fdev31/keypass/src/indexPage.h

#ifndef _INDEXPAGE_H
#define _INDEXPAGE_H
#include <Arduino.h>
#include <stdint.h>
#include <stddef.h>
const size_t index_html_gz_len = 7565;
const uint8_t index_html[7565] PROGMEM = {
0x1f, 0x8b, 0x08, 0x08, 0x08, 0xaf, 0xe2, 0x68, 0x02, 0x03, 0x69, 0x6e, 0x64, 0x65, 0x78, 0x2e,
0x68, 0x74, 0x6d, 0x6c, 0x00, 0xc4, 0x3c, 0x7b, 0x7f, 0x9b, 0x46, 0xb6, 0xff, 0xf3, 0x29, 0x26,
0x24, 0x75, 0xa0, 0x91, 0x64, 0x49, 0xb1, 0x13, 0x07, 0x8c, 0x5c, 0xe7, 0xd5, 0xb8, 0x9b, 0xd7,
0x8d, 0x9d, 0x76, 0xf7, 0xe6, 0x97, 0x1b, 0x23, 0x18, 0x49, 0x24, 0x08, 0x28, 0x20, 0xcb, 0xaa,
0xac, 0xfd, 0xec, 0xf7, 0x9c, 0x79, 0xc0, 0xf0, 0x90, 0xed, 0x76, 0xd3, 0x7b, 0xb7, 0x5b, 0x59,
0x0c, 0x33, 0x67, 0xce, 0xfb, 0x35, 0xa3, 0x1e, 0xde, 0x79, 0xfe, 0xee, 0xd9, 0xd9, 0xbf, 0xde,
0xbf, 0x20, 0xb3, 0x7c, 0x1e, 0x8e, 0xb4, 0x43, 0xf9, 0x87, 0xba, 0x3e, 0xfc, 0xc9, 0x83, 0x3c,
0xa4, 0xa3, 0x7f, 0xd0, 0xd5, 0x7b, 0x37, 0xcb, 0x0e, 0x77, 0xf9, 0xa3, 0x76, 0x38, 0xa7, 0xb9,
0x4b, 0x22, 0x77, 0x4e, 0x1d, 0xfd, 0x22, 0xa0, 0xcb, 0x24, 0x4e, 0x73, 0x9d, 0x78, 0x71, 0x94,
0xd3, 0x28, 0x77, 0xf4, 0x65, 0xe0, 0xe7, 0x33, 0xc7, 0xa7, 0x17, 0x81, 0x47, 0xbb, 0xec, 0xa1,
0x43, 0x82, 0x28, 0xc8, 0x03, 0x37, 0xec, 0x66, 0x9e, 0x1b, 0x52, 0x67, 0xd0, 0xeb, 0xeb, 0x64,
0x17, 0x00, 0x85, 0x41, 0xf4, 0x4d, 0x4b, 0x69, 0xe8, 0xe8, 0x59, 0xbe, 0x0a, 0x69, 0x36, 0xa3,
0x34, 0xd7, 0xb5, 0x59, 0x4a, 0x27, 0x8e, 0x3e, 0xcb, 0xf3, 0x24, 0xb3, 0x76, 0x77, 0x27, 0x00,
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
0x83, 0x9a, 0x0b, 0x8f, 0x05, 0x0f, 0xc0, 0x5a, 0xdd, 0x3c, 0xb8, 0x40, 0x85, 0xbb, 0xa0, 0xe9,
0x24, 0x44, 0x05, 0x9c, 0x05, 0xbe, 0x4f, 0xa3, 0x82, 0x3e, 0xcb, 0x1a, 0x53, 0x10, 0x0b, 0xb2,
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
};
#endif
