fdev31/keypass/src/password.cpp

#include "password.h"
#include "Preferences.h"
#include "WString.h"
#include "configuration.h"
#include "constants.h"
#include "crypto.h"
#include "graphics.h"
#include "hid.h"
#include "importexport.h"
#include "main.h"
#include "restore.h"
#include "settings.h"
#include "streamadapter.h"
#include "utils.h"
#include <Arduino.h>
#include <ESPAsyncWebServer.h>
#include <cstring>
#include <stdio.h>
#include <stdlib.h>
#include <string.h>
#include <time.h>
#include <unistd.h>

// Core business logic functions (independent of AsyncWebServerRequest)

Password password;

static Password readPassword(int id) {
#if USE_EEPROM_API
  Password password;
  int address = id * sizeof(Password);
  EEPROM.get(address, password);
  // Add validation check to ensure data is valid
  if (password.name[0] == 0xFF) { // EEPROM default state is 0xFF
    password.name[0] = '\0';      // Mark as empty
  }
  return password;
#else
  uint8_t passBuffer[MAX_PASS_LEN];
  uint8_t nonce[NONCE_LEN];
  Preferences preferences;
  const char *key = mkEntryName(id);
  preferences.begin(key, true);
  if (preferences.isKey(F_NAME) == false) {
    preferences.end();
    Password empty_password;
    empty_password.name[0] = '\0'; // No password found
    return empty_password;
  }
  int pass_version = preferences.getInt(F_FORMAT, -1);
  if (pass_version == 1) {
    strlcpy(password.name, preferences.getString(F_NAME).c_str(), MAX_NAME_LEN);
    preferences.getBytes(F_PASSWORD, passBuffer, MAX_PASS_LEN);
    preferences.getBytes(F_NONCE, nonce, NONCE_LEN);
    password.layout = preferences.getInt(F_LAYOUT);
  }
  preferences.end();

  if (pass_version == -1) {
    password.name[0] = '\0'; // No password found
  }

  switch (pass_version) {
  case 0:
    strlcpy((char *)password.password, (char *)passBuffer, MAX_PASS_LEN);
    break;
  case 1:
    decryptBuffer((uint8_t *)passBuffer, (char *)password.password,
                  MAX_PASS_LEN, nonce);
    break;
  }
  memset(passBuffer, 0, MAX_PASS_LEN);
  return password;
#endif
}

static void clearPassword(int id) {
  Preferences preferences;
  preferences.begin(mkEntryName(id), false);
  preferences.clear();
  preferences.end();
}

static void writePassword(int id, const Password &password) {
#if USE_EEPROM_API
  int address = id * sizeof(Password);
  EEPROM.put(address, password);
  EEPROM.commit();
#else
  uint8_t *nonce = getNonce();
  int pass_len = strlen((const char *)password.password);
  static uint8_t encrypted_password[MAX_PASS_LEN];
  Preferences preferences;

  preferences.begin(mkEntryName(id), false);
  preferences.putString(F_NAME, password.name);
  randomizeBuffer((uint8_t *)password.password + pass_len + 1,
                  MAX_PASS_LEN - pass_len - 1);
  encryptBuffer((char *)password.password, encrypted_password, MAX_PASS_LEN,
                nonce);
  preferences.putBytes(F_PASSWORD, encrypted_password, MAX_PASS_LEN);
  preferences.putBytes(F_NONCE, nonce, NONCE_LEN);
  preferences.putInt(F_FORMAT, FORMAT_VERSION);
  preferences.putInt(F_LAYOUT, password.layout);
  preferences.end();
  memset(encrypted_password, 0, MAX_PASS_LEN);
#endif
}

static void sendAnyKeymap(const char *text, int layout, int newline) {
  if (layout == -1) {
    while (*text) {
      sendKey(*text++, true);
    }

  } else {
    while (*text) {
      sendKeymap(*text++, layout);
      delay(50);
    }
  }
  if (newline) {
    sendKey('\n', false); // Send newline if requested
  }
}

bool typeRawText(const char *text, int layout, bool sendNewline) {
  if (text == nullptr)
    return false;

  ping();
  sendAnyKeymap(text, layout, sendNewline);
  return true;
}

bool typePassword(int id, int layout, bool sendNewline) {
  if (id < 0 || id >= MAX_PASSWORDS)
    return false;

  ping();

  // #ifdef ENABLE_GRAPHICS
  //   printText(1, "Typing");
  // #endif
  password = readPassword(id);
  char *text = (char *)password.password;

  // If layout is specified, use it; otherwise use the stored layout
  int effectiveLayout = (layout != -1) ? layout : password.layout;

  sendAnyKeymap(text, effectiveLayout, sendNewline);
  memset(password.password, 0, MAX_PASS_LEN);
  // #ifdef ENABLE_GRAPHICS
  //   printText(1, "Typed");
  // #endif
  return true;
}

const char *fetchPassword(int id) {
  if (id < 0 || id >= MAX_PASSWORDS)
    return nullptr;

  ping();
  password = readPassword(id);
  return (char *)password.password;
}

void clearFetchedPassword() { memset(password.password, 0, MAX_PASS_LEN); }

bool editPassword(int id, const char *name, const char *clear_pass,
                  int layout) {
  if (id < 0 || id >= MAX_PASSWORDS)
    return false;

  ping();

  password = readPassword(id);

  // Update fields if provided
  if (layout != -2) { // -2 means "don't change"
    password.layout = layout;
  }

  if (name != nullptr) {
    strlcpy(password.name, name, MAX_NAME_LEN);
  }

  if (clear_pass != nullptr) {
    strlcpy((char *)password.password, clear_pass, MAX_PASS_LEN);
  }

  // Save the updated password
  writePassword(id, password);
  memset(password.password, 0, MAX_PASS_LEN);
  return true;
}

String listPasswords() {
  ping();

  // Create a dynamic JSON string to hold the list of passwords
  String json = "{\"passwords\":[";

  // Loop through password ids and add existing passwords to the JSON
  bool firstItem = true;
  for (int id = 0; id < MAX_PASSWORDS; id++) {
    password = readPassword(id);
    if (password.name[0] == '\0')
      break;

    if (!firstItem) {
      json += ",";
    }
    json += "{\"name\":\"" + String(password.name) +
            "\",\"uid\":" + String(id) +
            ",\"layout\":" + String(password.layout) +
            ",\"len\":" + strlen((char *)password.password) + "}";
    firstItem = false;
  }
  clearFetchedPassword();

  Preferences prefs;
  size_t entries_left = prefs.freeEntries();
  json += String("], \"free\":") + entries_left + "}";

  return json;
}

void factoryReset() {
  ping();
  // #ifdef ENABLE_GRAPHICS
  //   printText(1, "Reset");
  // #endif
  Preferences preferences;

  for (int id = 0; id < MAX_PASSWORDS; id++) {
    clearPassword(id);
  }

#if not USE_EEPROM_API
  factoryResetSettings();
#elif
#pragma message "EEPROM API is used, factory reset not implemented for settings"
#endif
}

bool setupPassphrase(const char *phrase) {
  if (phrase == nullptr)
    return false;
  ping();
  return setPassPhrase(phrase);
}

bool dumpOnePassword(int id, StringStreamAdapter &pString) {
  Password password = readPassword(id);
  if (!password.name[0]) {
    return false;
  }

  dumpSinglePassword(pString, password.name, (const char *)password.password,
                     password.layout, getNonce());
  memset(password.password, 0, MAX_PASS_LEN);
  return true;
}

void dumpPasswords(StringStreamAdapter *stream) {
  ping();
  stream->write(DUMP_START "\n");

  StringStreamAdapter pString;

  bool endReached = false;
  for (int id = 0; !endReached && id < MAX_PASSWORDS; id++) {
    pString.clear();
    if (!dumpOnePassword(id, pString)) {
      endReached = true;
      break;
    }
    stream->write(pString.c_str());
    stream->write("\n");
  }
  stream->write(DUMP_END "\n");
}

static int savePassCount = 0;

void savePassData(const char *name, const char *passwordData, int layout,
                  int slot, uint8_t *nonce) {
  editPassword(slot, name, passwordData, layout);
  savePassCount++;
}

String restoreMCUPasswords(const String &data) {
  savePassCount = 0;
  restorePasswords(data, savePassData, true);
  return String("Restored ") + String(savePassCount) +
         " passwords successfully.";
}
