fdev31/keypass/src/captive.cpp

#include "settings.h"
#include "configuration.h"
#include <WiFi.h>
#include <string.h>

// Captive Portal
#include "main.h"
#include <AsyncTCP.h> //https://github.com/me-no-dev/AsyncTCP using the latest dev version from @me-no-dev
#include <DNSServer.h>
#include <ESPAsyncWebServer.h> //https://github.com/me-no-dev/ESPAsyncWebServer using the latest dev version from @me-no-dev
#include <esp_wifi.h>          //Used for mpdu_rx_disable android workaround

// Pre reading on the fundamentals of captive portals
// https://textslashplain.com/2022/06/24/captive-portals/

static const IPAddress localIP(4, 3, 2,
                               1); // the IP address the web server, Samsung
                                   // requires the IP to be in public space
static const IPAddress gatewayIP(4, 3, 2,
                                 1); // IP address of the network should be the
                                     // same as the local IP for captive portals
static const IPAddress subnetMask(255, 255, 255, 0);

static const String localIPURL = "http://4.3.2.1";

DNSServer dnsServer;
AsyncWebServer server(80);

void setUpDNSServer(const char *ssid, const char *password,
                    DNSServer &dnsServer, const IPAddress &localIP) {

  // Set the TTL for DNS response and start the DNS server
  dnsServer.setTTL(3600);
  dnsServer.start(53, "*", localIP);
}

void startSoftAccessPoint(const char *wifi_ssid, const char *wifi_password,
                          const IPAddress &localIP,
                          const IPAddress &gatewayIP) {
  // Define the WiFi channel to be used (channel 6 in this case)
#define WIFI_CHANNEL 6

  // Set the WiFi mode to access point and station
  WiFi.mode(WIFI_MODE_AP);

  // Define the subnet mask for the WiFi network
  const IPAddress subnetMask(255, 255, 255, 0);

  // Configure the soft access point with a specific IP and subnet mask
  WiFi.softAPConfig(localIP, gatewayIP, subnetMask);

  // Start the soft access point with the given ssid, password, channel, max
  // number of clients
  WiFi.softAP(wifi_ssid, wifi_password, WIFI_CHANNEL, 0, MAX_CLIENTS);

  // Disable AMPDU RX on the ESP32 WiFi to fix a bug on Android
  esp_wifi_stop();
  esp_wifi_deinit();
  wifi_init_config_t my_config = WIFI_INIT_CONFIG_DEFAULT();
  my_config.ampdu_rx_enable = false;
  esp_wifi_init(&my_config);
  esp_wifi_start();
  vTaskDelay(100 / portTICK_PERIOD_MS); // Add a small delay
}

void setUpWebserver(AsyncWebServer &server, const IPAddress &localIP) {
  //======================== Webserver ========================
  // WARNING IOS (and maybe macos) WILL NOT POP UP IF IT CONTAINS THE WORD
  // "Success" https://www.esp8266.com/viewtopic.php?f=34&t=4398 SAFARI (IOS) IS
  // STUPID, G-ZIPPED FILES CAN'T END IN .GZ
  // https://github.com/homieiot/homie-esp8266/issues/476 this is fixed by the
  // webserver serve static function. SAFARI (IOS) there is a 128KB limit to the
  // size of the HTML. The HTML can reference external resources/images that
  // bring the total over 128KB SAFARI (IOS) popup browser has some severe
  // limitations (javascript disabled, cookies disabled)

  // Required
  server.on("/connecttest.txt", [](AsyncWebServerRequest *request) {
    request->redirect("http://logout.net");
    ping();
  }); // windows 11 captive portal workaround
  server.on("/wpad.dat", [](AsyncWebServerRequest *request) {
    request->send(404);
  }); // Honestly don't understand what this is but a 404 stops win 10 keep
      // calling this repeatedly and panicking the esp32 :)

  // Background responses: Probably not all are Required, but some are. Others
  // might speed things up? A Tier (commonly used by modern systems)
  server.on("/generate_204", [](AsyncWebServerRequest *request) {
    request->redirect(localIPURL);
    ping();
  }); // android captive portal redirect
  server.on("/redirect", [](AsyncWebServerRequest *request) {
    request->redirect(localIPURL);
    ping();
  }); // microsoft redirect
  server.on("/hotspot-detect.html", [](AsyncWebServerRequest *request) {
    request->redirect(localIPURL);
    ping();
  }); // apple call home
  server.on("/canonical.html", [](AsyncWebServerRequest *request) {
    request->redirect(localIPURL);
    ping();
  }); // firefox captive portal call home
  server.on("/success.txt", [](AsyncWebServerRequest *request) {
    request->send(200);
    ping();
  }); // firefox captive portal call home
  server.on("/ncsi.txt", [](AsyncWebServerRequest *request) {
    request->redirect(localIPURL);
    ping();
  }); // windows call home

  // return 404 to webpage icon
  server.on("/favicon.ico", [](AsyncWebServerRequest *request) {
    request->send(404);
    ping();
  }); // webpage icon
  //

  // the catch all
  server.onNotFound([](AsyncWebServerRequest *request) {
    ping();
    request->redirect(localIPURL);
  });
};
static void handleWifiEvent(void *arg, esp_event_base_t event_base,
                            int32_t event_id, void *event_data) {
  if (event_base == WIFI_EVENT) {
    switch (event_id) {
    case WIFI_EVENT_AP_STACONNECTED:
    case WIFI_EVENT_AP_STADISCONNECTED:
    case WIFI_EVENT_AP_START:
      ping(); // Reset sleeping state
      break;
    }
  }
}

void captiveSetup() {
  String password = getWifiPassword();
  startSoftAccessPoint(DEFAULT_WIFI_SSID, password.c_str(), localIP, gatewayIP);
  setUpDNSServer(DEFAULT_WIFI_SSID, password.c_str(), dnsServer, localIP);
  setUpWebserver(server, localIP);
  server.begin();
  //
  esp_event_handler_register(WIFI_EVENT, ESP_EVENT_ANY_ID, &handleWifiEvent,
                             NULL); // Register event handler
}
void captiveLoop() {
  dnsServer.processNextRequest(); // I call this at least every 10ms in my other
}
