fdev31/keypass/src/keymap.cpp

#include "keymap.h"// FR keyboard layout
static const KeyMapping LAYOUT_FR[] = {
    {'\t', 43, 0},  // Tab
    {'\n', 40, 0},  // Enter
    {' ', 44, 0},    // Space
    {60, 100, 0}, // <
    {62, 100, 2}, // >
    {113, 4, 0}, // q
    {81, 4, 2}, // Q
    {98, 5, 0}, // b
    {66, 5, 2}, // B
    {99, 6, 0}, // c
    {67, 6, 2}, // C
    {100, 7, 0}, // d
    {68, 7, 2}, // D
    {101, 8, 0}, // e
    {69, 8, 2}, // E
    {102, 9, 0}, // f
    {70, 9, 2}, // F
    {103, 10, 0}, // g
    {71, 10, 2}, // G
    {104, 11, 0}, // h
    {72, 11, 2}, // H
    {105, 12, 0}, // i
    {73, 12, 2}, // I
    {106, 13, 0}, // j
    {74, 13, 2}, // J
    {107, 14, 0}, // k
    {75, 14, 2}, // K
    {108, 15, 0}, // l
    {76, 15, 2}, // L
    {44, 16, 0}, // ,
    {63, 16, 2}, // ?
    {110, 17, 0}, // n
    {78, 17, 2}, // N
    {111, 18, 0}, // o
    {79, 18, 2}, // O
    {112, 19, 0}, // p
    {80, 19, 2}, // P
    {97, 20, 0}, // a
    {65, 20, 2}, // A
    {114, 21, 0}, // r
    {82, 21, 2}, // R
    {115, 22, 0}, // s
    {83, 22, 2}, // S
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
    {0, 0, 0}  // End marker
};

// US keyboard layout
static const KeyMapping LAYOUT_US[] = {
    {'\t', 43, 0},  // Tab
    {'\n', 40, 0},  // Enter
    {' ', 44, 0},    // Space
    {97, 4, 0}, // a
    {65, 4, 2}, // A
    {98, 5, 0}, // b
    {66, 5, 2}, // B
    {99, 6, 0}, // c
    {67, 6, 2}, // C
    {100, 7, 0}, // d
    {68, 7, 2}, // D
    {101, 8, 0}, // e
    {69, 8, 2}, // E
    {102, 9, 0}, // f
    {70, 9, 2}, // F
    {103, 10, 0}, // g
    {71, 10, 2}, // G
    {104, 11, 0}, // h
    {72, 11, 2}, // H
    {105, 12, 0}, // i
    {73, 12, 2}, // I
    {106, 13, 0}, // j
    {74, 13, 2}, // J
    {107, 14, 0}, // k
    {75, 14, 2}, // K
    {108, 15, 0}, // l
    {76, 15, 2}, // L
    {109, 16, 0}, // m
    {77, 16, 2}, // M
    {110, 17, 0}, // n
    {78, 17, 2}, // N
    {111, 18, 0}, // o
    {79, 18, 2}, // O
    {112, 19, 0}, // p
    {80, 19, 2}, // P
    {113, 20, 0}, // q
    {81, 20, 2}, // Q
    {114, 21, 0}, // r
    {82, 21, 2}, // R
    {115, 22, 0}, // s
    {83, 22, 2}, // S
    {116, 23, 0}, // t
    {84, 23, 2}, // T
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
    {0, 0, 0}  // End marker
};

// Array of pointers to keyboard layouts for easy access
const KeyMapping* KEYBOARD_LAYOUTS[] = {
    LAYOUT_FR,
    LAYOUT_US
};
