fdev31/keypass/src/constants.h

// constants.h
#ifndef _CONSTANTS_H
#define _CONSTANTS_H

#define FORMAT_VERSION 1

// TODO: measure the maximum acceptable number more accurately
#define MAX_PASSWORDS 100
#define STORED_PASSWD_BLOCKS 2

// Crypto constants
#define STO_BLOCK_SIZE 16
#define RAND_BYTE_FACTOR RAND_MAX / 255

#define CRYPTO_HEADER_SIZE 2 // salt + layout

#define META_SIZE 32
#define NONCE_LEN 12
#define MAX_NAME_LEN META_SIZE - CRYPTO_HEADER_SIZE
#define MAX_PASS_LEN (STORED_PASSWD_BLOCKS * 16)

#define CRYPTO_OVERHEAD 0
#define UNENCRYPTED_DATA_LENGTH 1 + NONCE_LEN // version + nonce

// Encrypted dump length
#define DUMP_LENGTH (META_SIZE + MAX_PASS_LEN + CRYPTO_OVERHEAD)
static_assert(DUMP_LENGTH % STO_BLOCK_SIZE == 0,
              "DUMP_LENGTH must be a multiple of STO_BLOCK_SIZE");

// Preferences fields
#define F_NAMESPACE "KeyPass" // used for global settings
#define DEVICE_NAME_KEY "device_name"
#define WIFI_PASSWORD_KEY "wifi_password"
#define MAGIC_KEY_KEY "magic_key"
// password entry properties
#define F_NAME "name"
#define F_PASSWORD "password"
#define F_FORMAT "v"
#define F_LAYOUT "layout"
#define F_NONCE "n"

#define DUMP_START "#KPDUMP"
#define DUMP_END "#/KPDUMP"

#endif // CONSTANTS_H
