fdev31/keypass/src/icons.cpp

// Generated bitmap icons implementation
#include "icons.h"

// Bitmap data for icon_bluetooth.png (20x20)
const uint8_t icon_bluetooth_data[] = {
    0x00, 0x00, 0x00, 0x00, 0x06, 0x00, 0x00, 0x0E, 0x00, 0x00, 0x1E, 0x00,
    0x00, 0x36, 0x00, 0x30, 0xE6, 0x00, 0x60, 0x66, 0x00, 0xC0, 0x36, 0x00,
    0x80, 0x1F, 0x00, 0x00, 0x0F, 0x00, 0x00, 0x0F, 0x00, 0x80, 0x1F, 0x00,
    0xC0, 0x36, 0x00, 0x60, 0x66, 0x00, 0x30, 0x66, 0x00, 0x00, 0x36, 0x00,
    0x00, 0x1E, 0x00, 0x00, 0x0E, 0x00, 0x00, 0x06, 0x00, 0x00, 0x00, 0x00,
};
const Bitmap icon_bluetooth = {
    .data = icon_bluetooth_data,
    .width = 20,
    .height = 20
};

// Bitmap data for icon_wifi.png (20x20)
const uint8_t icon_wifi_data[] = {
    0x00, 0x00, 0x00, 0x00, 0x00, 0x00, 0x00, 0x06, 0x00, 0xE0, 0x7F, 0x00,
    0xF8, 0xF0, 0x01, 0x1E, 0x80, 0x07, 0x07, 0x06, 0x0E, 0xC3, 0x3F, 0x0C,
    0xF0, 0xF0, 0x00, 0x38, 0xC0, 0x01, 0x08, 0x06, 0x01, 0x80, 0x1F, 0x00,
    0xC0, 0x39, 0x00, 0x00, 0x00, 0x00, 0x00, 0x06, 0x00, 0x00, 0x06, 0x00,
    0x00, 0x06, 0x00, 0x00, 0x00, 0x00, 0x00, 0x00, 0x00, 0x00, 0x00, 0x00,
};
const Bitmap icon_wifi = {
    .data = icon_wifi_data,
    .width = 20,
    .height = 20
};

// Bitmap data for icon_up.png (20x20)
const uint8_t icon_up_data[] = {
    0x00, 0x00, 0x00, 0x00, 0x06, 0x00, 0x00, 0x0F, 0x00, 0x80, 0x1F, 0x00,
    0xC0, 0x3F, 0x00, 0xE0, 0x7F, 0x00, 0xF0, 0xFF, 0x00, 0xF8, 0xFF, 0x01,
    0xFC, 0xFF, 0x03, 0xFE, 0xFF, 0x07, 0xFE, 0xFF, 0x07, 0x80, 0x1F, 0x00,
    0x80, 0x1F, 0x00, 0x80, 0x1F, 0x00, 0x80, 0x1F, 0x00, 0x80, 0x1F, 0x00,
    0x80, 0x1F, 0x00, 0x80, 0x1F, 0x00, 0x80, 0x1F, 0x00, 0x00, 0x00, 0x00,
};
const Bitmap icon_up = {
    .data = icon_up_data,
    .width = 20,
    .height = 20
};

// Bitmap data for icon_down.png (20x20)
const uint8_t icon_down_data[] = {
    0x00, 0x00, 0x00, 0x80, 0x1F, 0x00, 0x80, 0x1F, 0x00, 0x80, 0x1F, 0x00,
    0x80, 0x1F, 0x00, 0x80, 0x1F, 0x00, 0x80, 0x1F, 0x00, 0x80, 0x1F, 0x00,
    0x80, 0x1F, 0x00, 0xFE, 0xFF, 0x07, 0xFE, 0xFF, 0x07, 0xFC, 0xFF, 0x03,
    0xF8, 0xFF, 0x01, 0xF0, 0xFF, 0x00, 0xE0, 0x7F, 0x00, 0xC0, 0x3F, 0x00,
    0x80, 0x1F, 0x00, 0x00, 0x0F, 0x00, 0x00, 0x06, 0x00, 0x00, 0x00, 0x00,
};
const Bitmap icon_down = {
    .data = icon_down_data,
    .width = 20,
    .height = 20
};

// Collection of all bitmap icons
const Bitmap* icons[] = {
    &icon_bluetooth,
    &icon_wifi,
    &icon_up,
    &icon_down,
};
