fdev31/keypass/scripts/genkeymaps.py

#!/bin/env python
import argparse
import os
import sys
import glob
from pathlib import Path


def parse_keymap_file(filename):
    layout_name = Path(filename).stem.upper()
    results: list[dict[str, tuple[int, int]]] = []
    current_file = None

    code_map = {
        0: 0,
        1: 2,
        2: 64,
    }

    collected: dict[str, tuple[int, int]] = {}
    for line in open(filename).readlines():
        try:
            letters, code_str = line.strip().split(" ")
            code = int(code_str)
        except ValueError:
            sys.stderr.write(f"skipping bogus: <{line.strip()}>\n")
            continue
        code = int(code)
        for i, c in enumerate(letters):
            to_skip = False
            if c in collected:
                if collected[c] != (code, i):
                    if collected[c][1] > i:
                        sys.stderr.write(
                            f"Replacing {c} using code {(code, code_map[i])} - already defined as {collected[c]} !\n"
                        )
                    else:
                        sys.stderr.write(
                            f"Skipping duplicate for {c} using code {code} - already defined as {collected[c]} !\n"
                        )
                        to_skip = True

            if not to_skip:
                collected[c] = (code, code_map[i] if i else 0)
    results.append(collected)

    def convert_res(key_mapping):
        return [(k, v[0], v[1]) for k, v in key_mapping.items()]

    return layout_name, convert_res(results[0])


def generate_keymap_files(layout_data, prefix):
    """Generate the .h and .cpp files from the parsed layout data"""
    header = """#ifndef __CUSTOM_KEYMAP
#define __CUSTOM_KEYMAP
#include <stdint.h>

// Define a struct for each key mapping
typedef struct {
    uint8_t ascii;     // ASCII code
    uint8_t keycode;   // HID key code
    uint8_t modifier;  // Modifier key
} KeyMapping;

// Enum for supported layouts
typedef enum {
"""
    enum_values = []
    for i, (layout_name, _) in enumerate(layout_data):
        enum_values.append(f"    KBLAYOUT_{layout_name} = {i}")

    header += ",\n".join(enum_values) + "\n} KeyboardLayout;\n\n"

    header += "\nextern const KeyMapping* KEYBOARD_LAYOUTS[];\n"

    header += "#endif // __CUSTOM_KEYMAP\n"

    implementation = f'#include "{prefix}.h"'
    for layout_name, mappings in layout_data:
        implementation += f"// {layout_name} keyboard layout\n"
        implementation += f"static const KeyMapping LAYOUT_{layout_name}[] = {{\n"

        implementation += "    {'\\t', 43, 0},  // Tab\n"
        implementation += "    {'\\n', 40, 0},  // Enter\n"
        implementation += "    {' ', 44, 0},    // Space\n"

        for char, keycode, modifier in mappings:
            if char not in " \t\n\\":
                implementation += (
                    f"    {{{ord(char)}, {keycode}, {modifier}}}, // {char}\n"
                )
            else:
                implementation += f"    {{{ord(char)}, {keycode}, {modifier}}},"

        implementation += "    {0, 0, 0}  // End marker\n};\n\n"

    implementation += "// Array of pointers to keyboard layouts for easy access\n"
    implementation += "const KeyMapping* KEYBOARD_LAYOUTS[] = {\n"
    layout_pointers = []
    for layout_name, _ in layout_data:
        layout_pointers.append(f"    LAYOUT_{layout_name}")
    implementation += ",\n".join(layout_pointers) + "\n};\n\n"

    return header, implementation


def main():
    parser = argparse.ArgumentParser(
        description="Generate keymap header and implementation files."
    )
    parser.add_argument("inputs", nargs="+", help="Keymap directory or files")
    parser.add_argument(
        "-o", "--output", required=True, help="Output file prefix (e.g., ./src/icons)"
    )
    args = parser.parse_args()

    layout_data = []

    for path_arg in args.inputs:
        if os.path.isdir(path_arg):
            files = glob.glob(os.path.join(path_arg, "*"))
            for file in files:
                if os.path.isfile(file):
                    try:
                        layout_name, mappings = parse_keymap_file(file)
                        layout_data.append((layout_name, mappings))
                        print(
                            f"Processed {file}: {len(mappings)} mappings",
                            file=sys.stderr,
                        )
                    except Exception as e:
                        print(f"Error processing {file}: {str(e)}", file=sys.stderr)
        elif os.path.isfile(path_arg):
            try:
                layout_name, mappings = parse_keymap_file(path_arg)
                layout_data.append((layout_name, mappings))
                print(
                    f"Processed {path_arg}: {len(mappings)} mappings", file=sys.stderr
                )
            except Exception as e:
                print(f"Error processing {path_arg}: {str(e)}", file=sys.stderr)
                raise
        else:
            print(
                f"Warning: {path_arg} is not a valid file or directory", file=sys.stderr
            )

    if not layout_data:
        print("Error: No valid keymap files found", file=sys.stderr)
        return 1

    header, implementation = generate_keymap_files(layout_data, args.output)

    header_file = f"{args.output}.h"
    implementation_file = f"{args.output}.cpp"

    with open(header_file, "w") as h_file:
        h_file.write(header)

    with open(implementation_file, "w") as cpp_file:
        cpp_file.write(implementation)

    print(f"Generated {header_file} and {implementation_file}")
    return 0


if __name__ == "__main__":
    sys.exit(main())
